marianelavflora/medidores-de-anillos/3 - Medidores sueltos (US 0 a 16)/US_3.stl

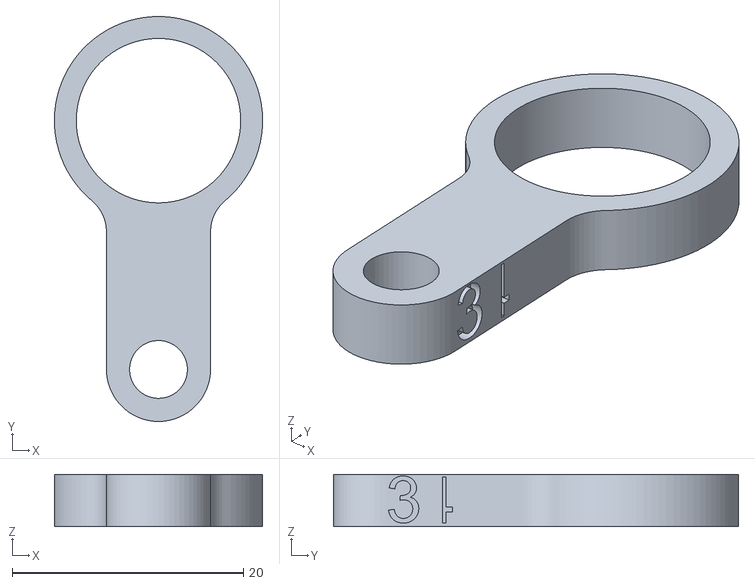
[picture p23: CAD file, 2026-10-04]
3 - Medidores sueltos (US 0 a 16)/US_3.stl
18.0 x 35.0 x 4.50
