marianelavflora/medidores-de-anillos/3 - Medidores sueltos (US 0 a 16)/US_15.5.stl

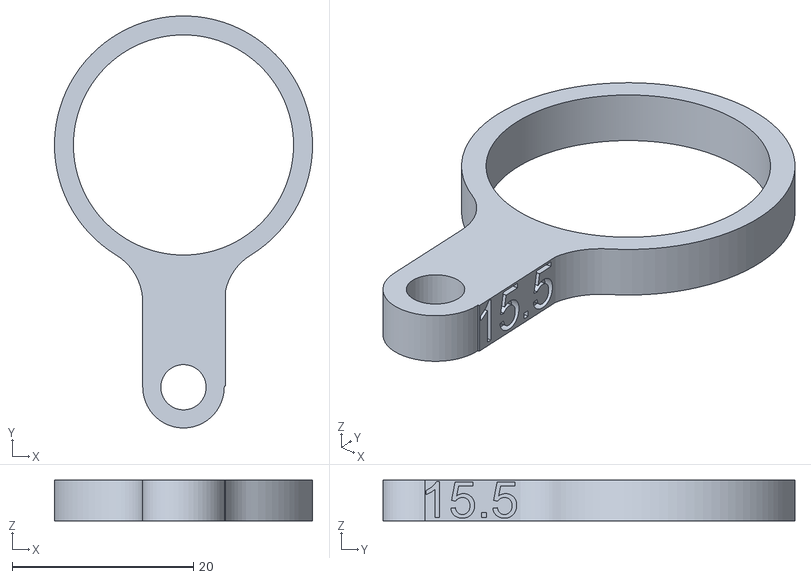
[picture p24: CAD file, 2026-10-04]
3 - Medidores sueltos (US 0 a 16)/US_15.5.stl
28.5 x 45.5 x 4.50
