marianelavflora/medidores-de-anillos/3 - Medidores sueltos (US 0 a 16)/US_14.stl

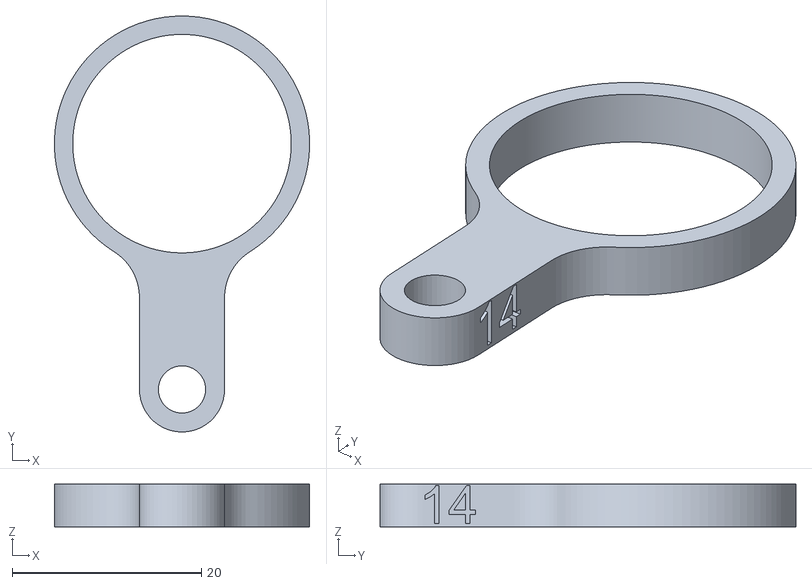
[picture p25: CAD file, 2026-10-04]
3 - Medidores sueltos (US 0 a 16)/US_14.stl
27.0 x 44.0 x 4.50
