marianelavflora/medidores-de-anillos/3 - Medidores sueltos (US 0 a 16)/US_8.stl

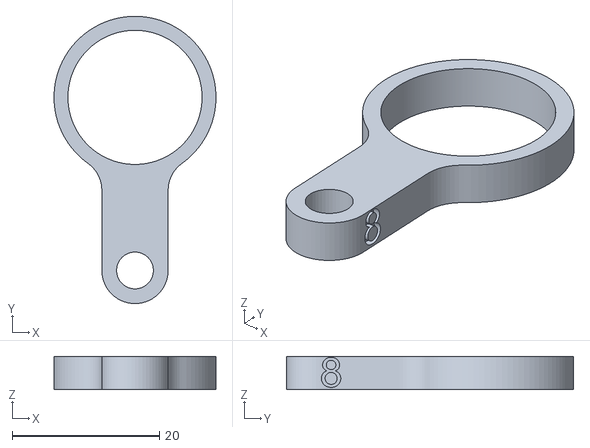
[picture p26: CAD file, 2026-10-04]
3 - Medidores sueltos (US 0 a 16)/US_8.stl
22.0 x 39.0 x 4.50
