marianelavflora/medidores-de-anillos/3 - Medidores sueltos (US 0 a 16)/US_0.5.stl

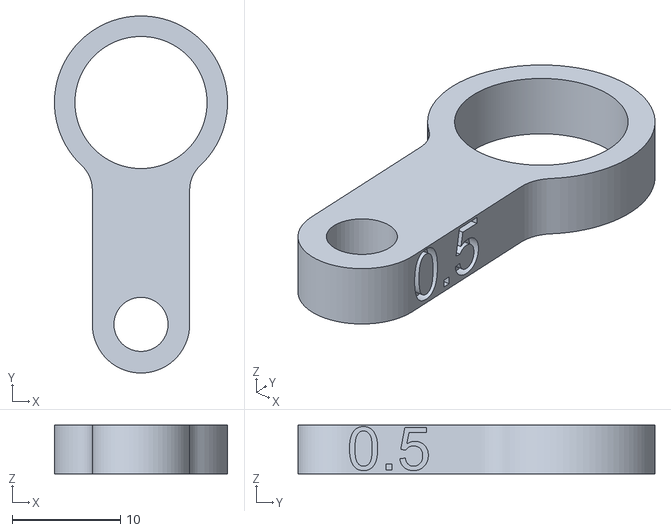
[picture p27: CAD file, 2026-10-04]
3 - Medidores sueltos (US 0 a 16)/US_0.5.stl
16.0 x 33.0 x 4.50
