marianelavflora/medidores-de-anillos/3 - Medidores sueltos (US 0 a 16)/US_13.stl

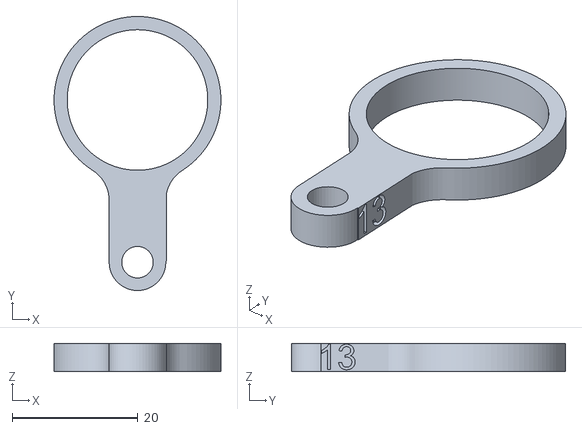
[picture p28: CAD file, 2026-10-04]
3 - Medidores sueltos (US 0 a 16)/US_13.stl
26.5 x 43.5 x 4.50
