marianelavflora/medidores-de-anillos/3 - Medidores sueltos (US 0 a 16)/US_9.stl

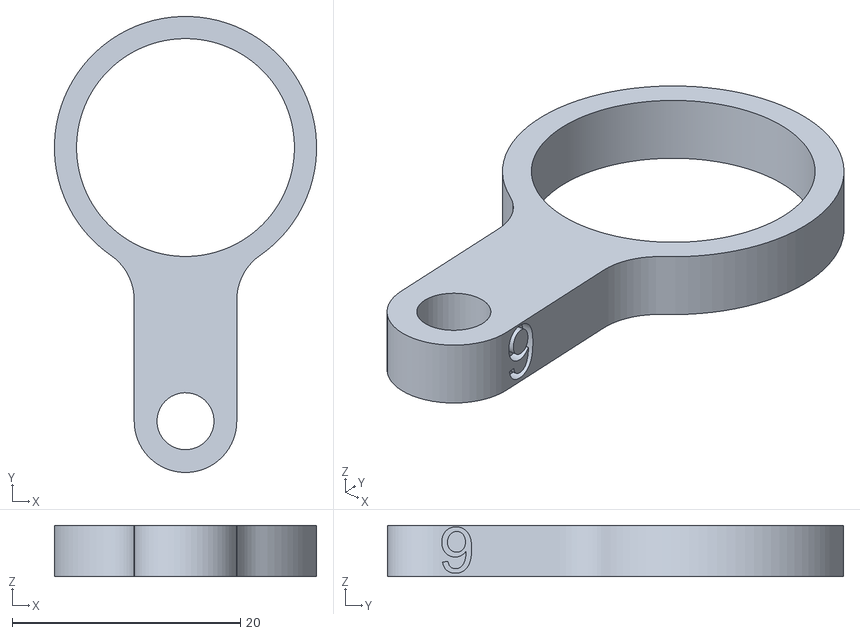
[picture p29: CAD file, 2026-10-04]
3 - Medidores sueltos (US 0 a 16)/US_9.stl
23.0 x 40.0 x 4.50
