marianelavflora/medidores-de-anillos/3 - Medidores sueltos (US 0 a 16)/US_12.stl

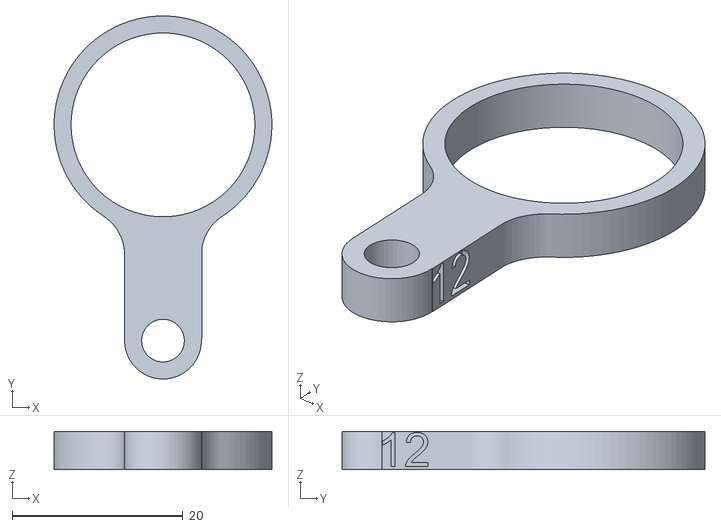
[picture p30: CAD file, 2026-10-04]
3 - Medidores sueltos (US 0 a 16)/US_12.stl
25.5 x 42.5 x 4.50
