marianelavflora/medidores-de-anillos/3 - Medidores sueltos (US 0 a 16)/US_2.stl

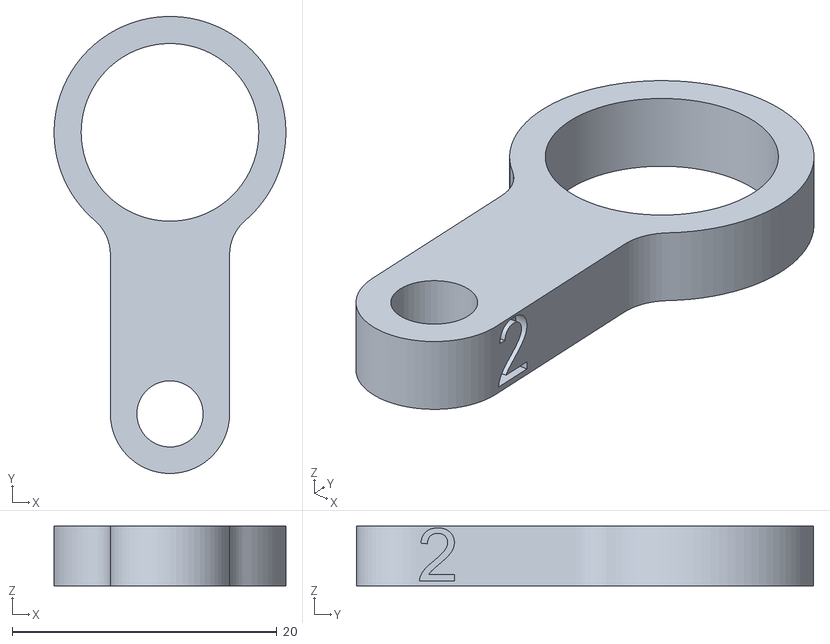
[picture p31: CAD file, 2026-10-04]
3 - Medidores sueltos (US 0 a 16)/US_2.stl
17.5 x 34.5 x 4.50
