marianelavflora/medidores-de-anillos/3 - Medidores sueltos (US 0 a 16)/US_9.5.stl

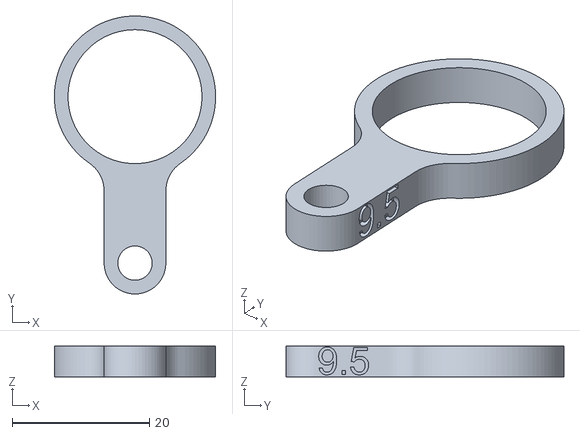
[picture p32: CAD file, 2026-10-04]
3 - Medidores sueltos (US 0 a 16)/US_9.5.stl
23.5 x 40.5 x 4.50
